leo96it/Tesi_webApp/Extras/PCB estimate.PNG

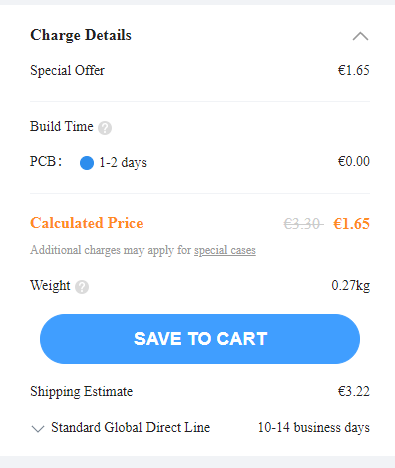
Extras/PCB estimate.PNG
