leo96it/Tesi_webApp/Frontend/angular-app/src/assets/machineryImage/002ufjd.png

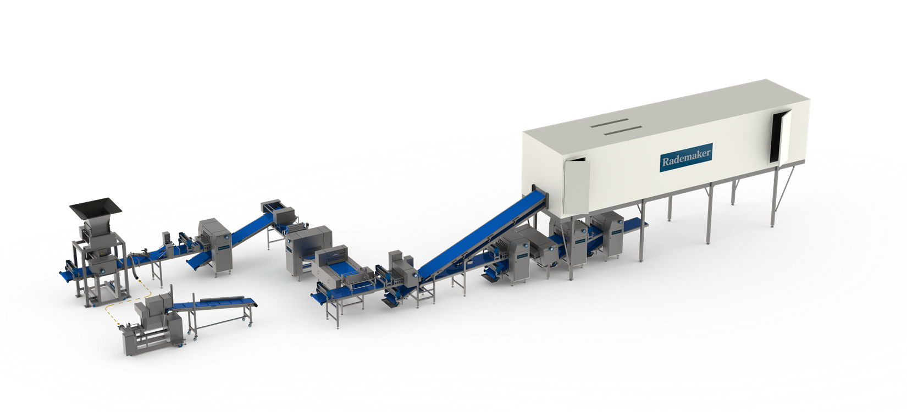
Frontend/angular-app/src/assets/machineryImage/002ufjd.png
