leo96it/Tesi_webApp/Frontend/angular-app/src/assets/machineryImage/003hghj.png

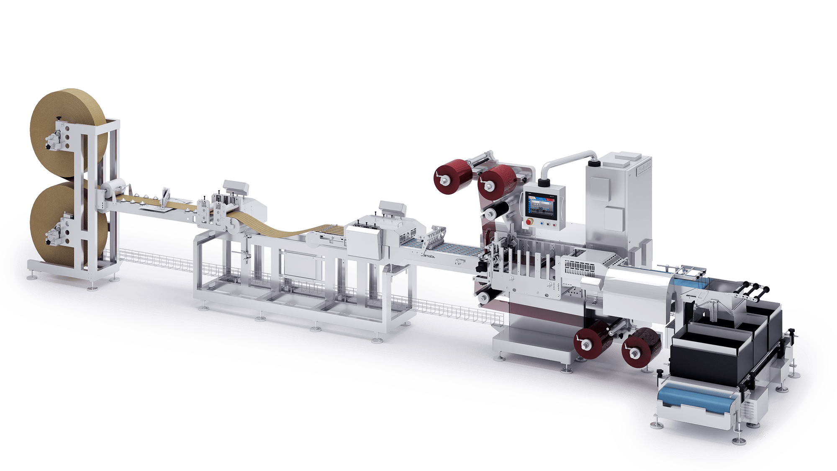
Frontend/angular-app/src/assets/machineryImage/003hghj.png
