leo96it/Tesi_webApp/Frontend/angular-app/src/assets/machineryImage/004hkhi.png

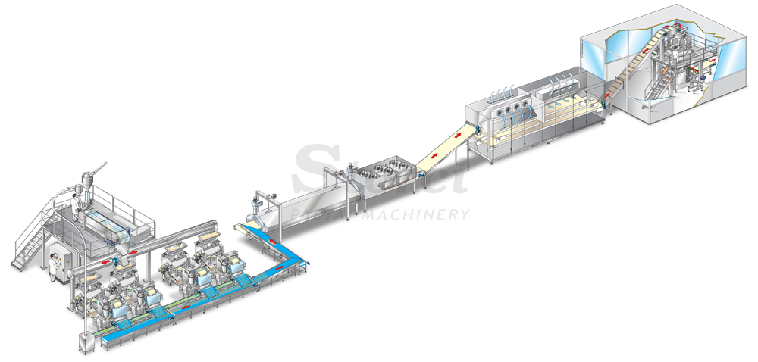
Frontend/angular-app/src/assets/machineryImage/004hkhi.png
