leo96it/Tesi_webApp/Frontend/angular-app/src/assets/machineryImage/006dewf.png

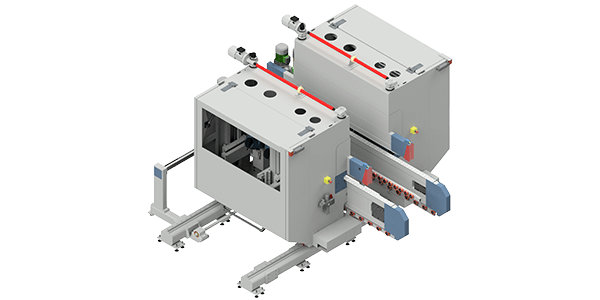
Frontend/angular-app/src/assets/machineryImage/006dewf.png
