leo96it/Tesi_webApp/Frontend/angular-app/src/assets/productImage/biellaNEMA.png

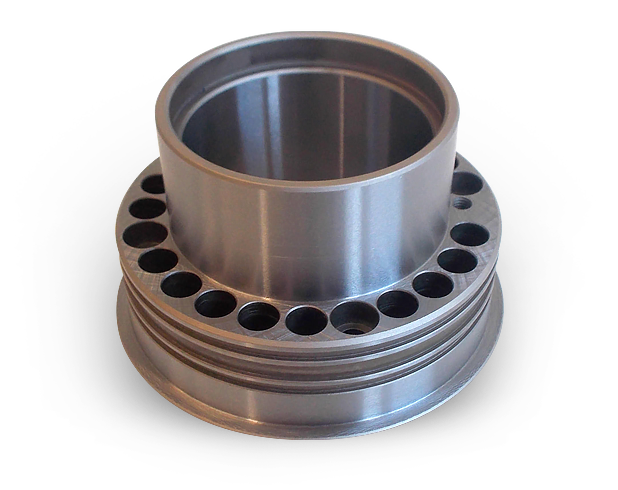
Frontend/angular-app/src/assets/productImage/biellaNEMA.png
