leo96it/Tesi_webApp/Frontend/angular-app/src/assets/productImage/giunto4p.png

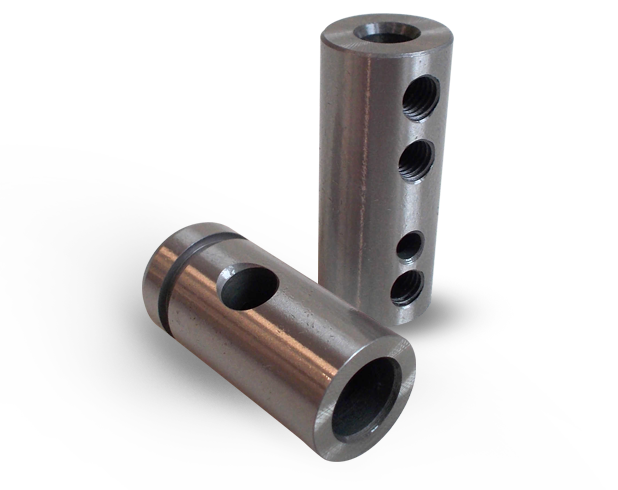
Frontend/angular-app/src/assets/productImage/giunto4p.png
