leo96it/Tesi_webApp/Frontend/angular-app/src/assets/productImage/piastra-perno.png

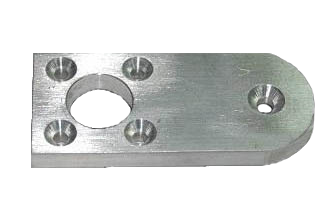
Frontend/angular-app/src/assets/productImage/piastra-perno.png
