leo96it/Tesi_webApp/Frontend/angular-app/src/assets/productImage/piastra-slitta.png

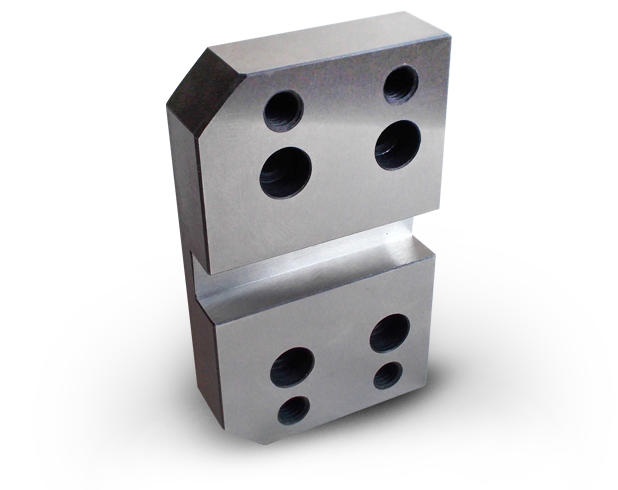
Frontend/angular-app/src/assets/productImage/piastra-slitta.png
