leo96it/Tesi_webApp/Frontend/angular-app/src/assets/productImage/supporto3rf.png

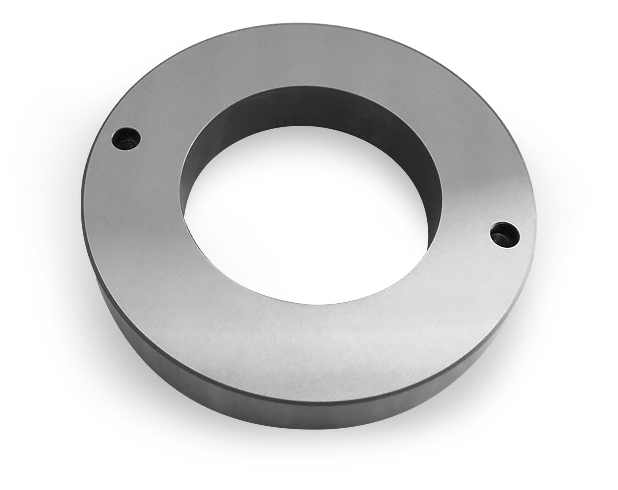
Frontend/angular-app/src/assets/productImage/supporto3rf.png
